Bharat2310/sih-2026/assets/screenshots/after_dac_waveform.jpeg

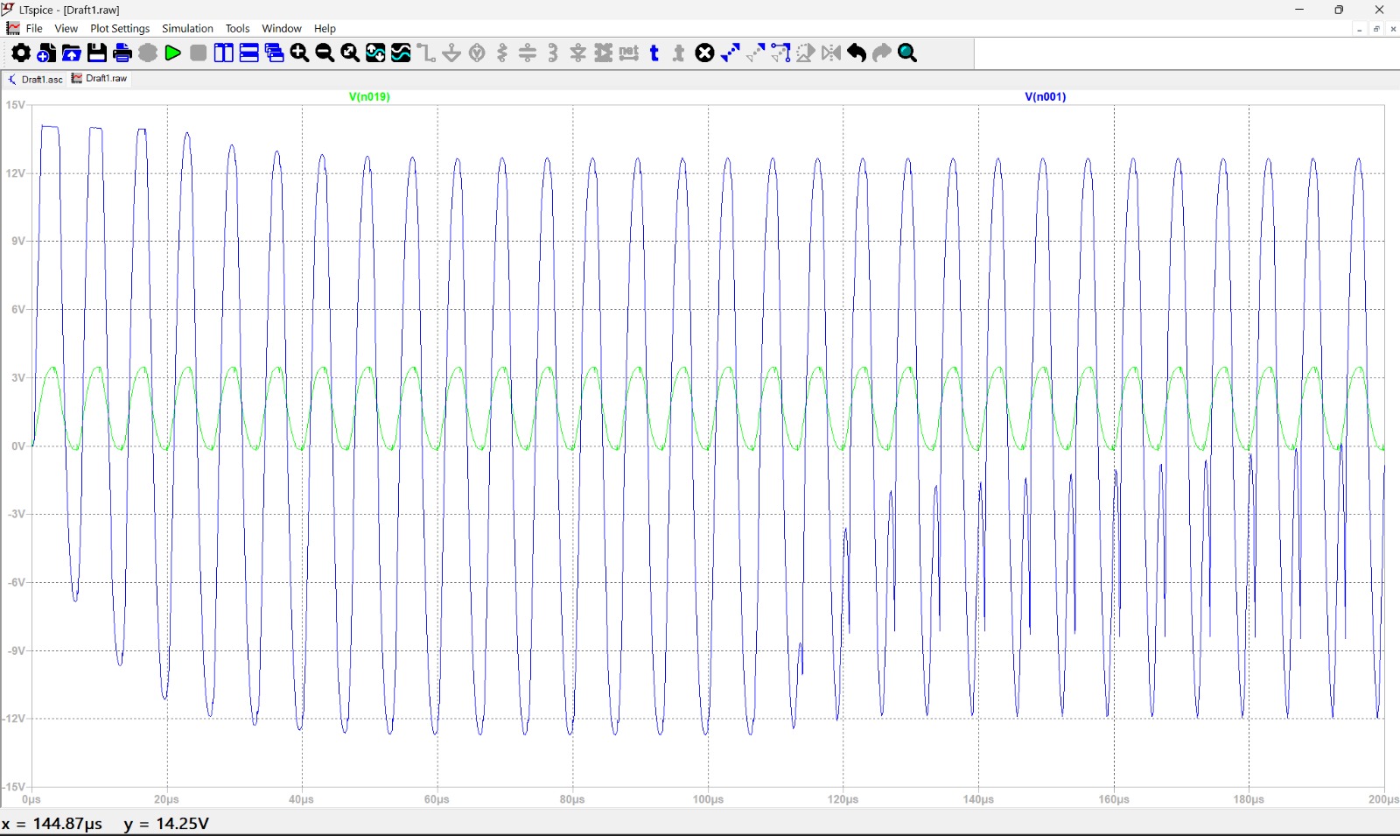
assets/screenshots/after_dac_waveform.jpeg
