Bharat2310/sih-2026/assets/screenshots/before_dac_full_pipeline.png

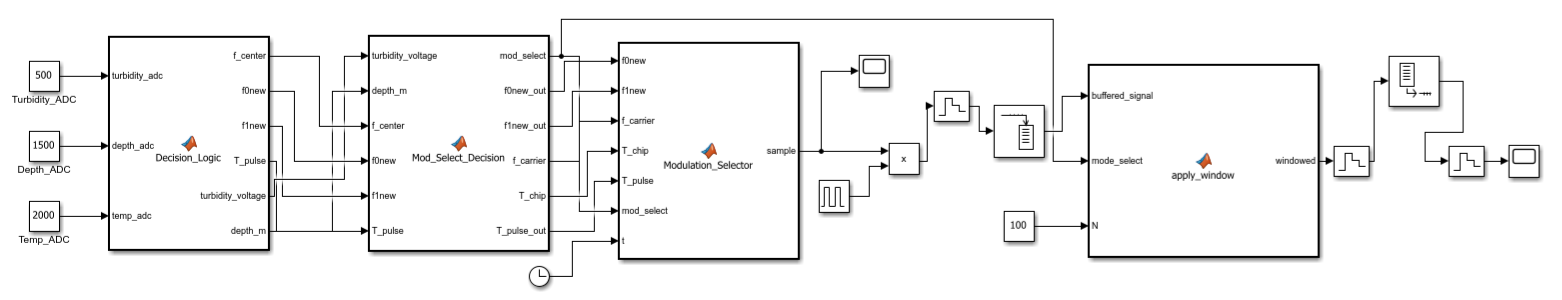
assets/screenshots/before_dac_full_pipeline.png
