Bharat2310/sih-2026/assets/screenshots/mod_select_decision.jpeg

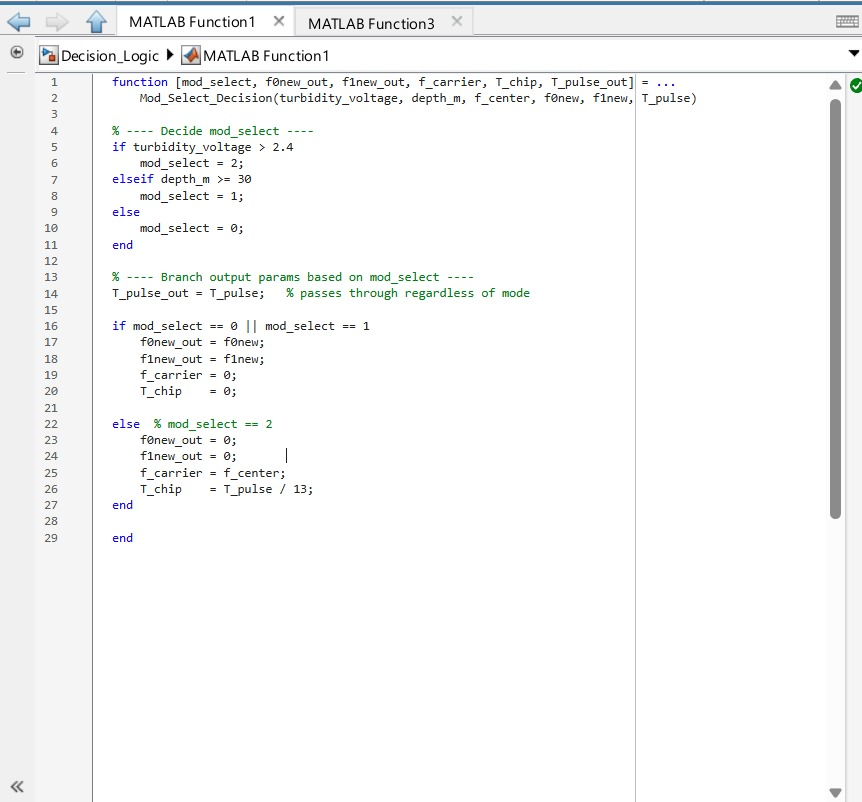
assets/screenshots/mod_select_decision.jpeg
