Bharat2310/sih-2026/assets/screenshots/mode0_lfm_final.jpeg

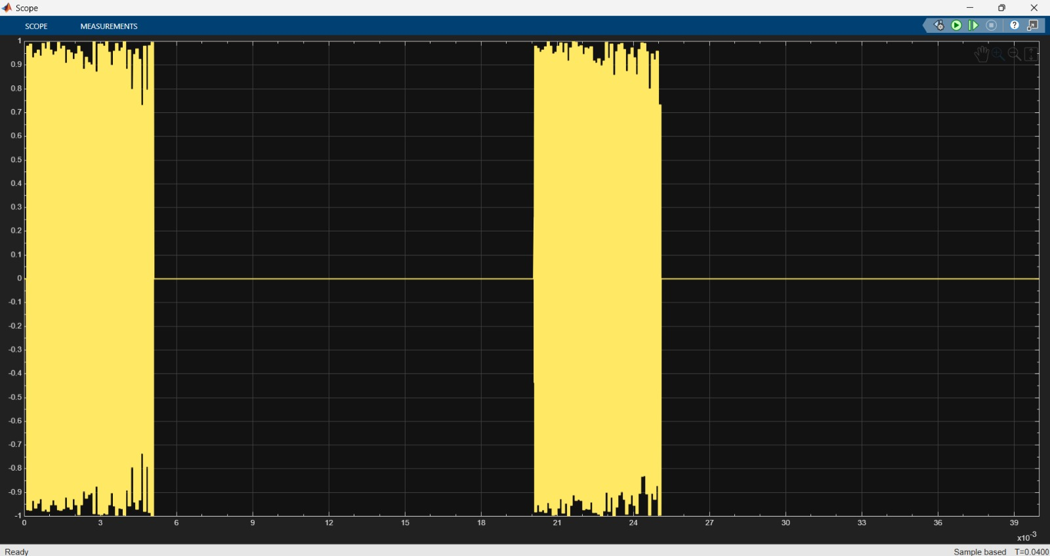
assets/screenshots/mode0_lfm_final.jpeg
