Bharat2310/sih-2026/assets/screenshots/mode2_phasecoded_raw.jpeg

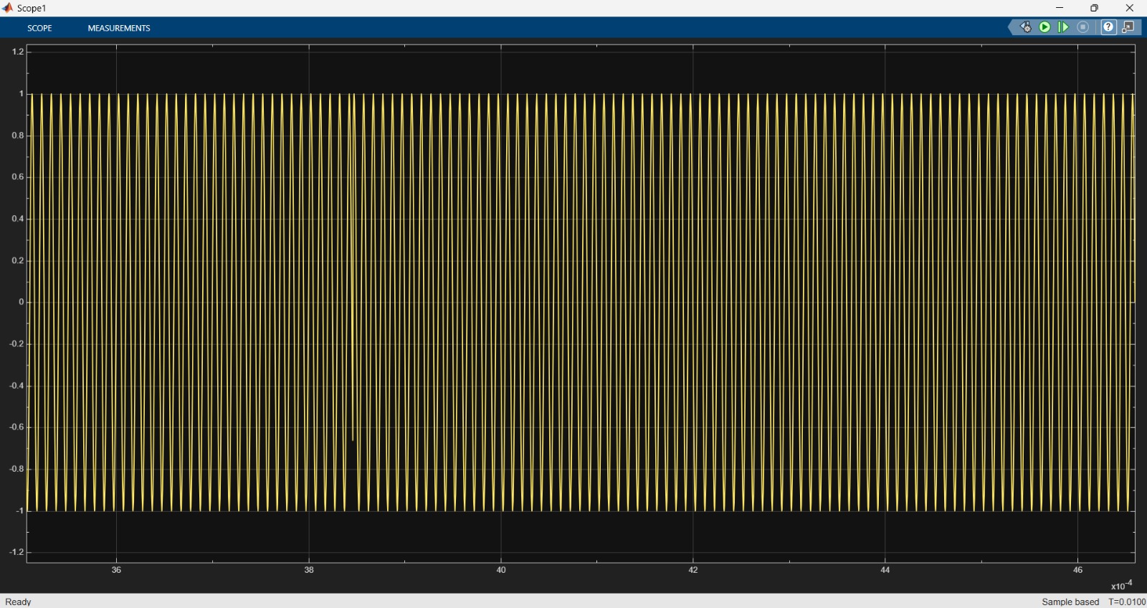
assets/screenshots/mode2_phasecoded_raw.jpeg
