Bharat2310/sih-2026/src/ltspice/after_dac_model.asc

C1: cap; 1n
C2: cap; 1n
C3: cap; 100p
C4: cap; 10µ
D1: diode
D2: diode
L1: ind; 11.26m
L2: ind; 1.126m
Q1: npn
Q2: pnp
R1: res; 10k
R2: res; 6.2k
R3: res; 1k
R4: res; 100
S1: sw; MUX
S2: sw; MUX
S3: sw; MUX
S4: sw; MUX
S5: sw; MUX
S6: sw; MUX
U1: LT1122
V1: voltage; PULSE(0 3.3 0 10n 10n 3.33u 6.66u)
V2: voltage; 0
V3: voltage; 3.3
V4: voltage; 0
V5: voltage; 5
V6: voltage; 18
V7: voltage; -18
V8: voltage; 18
V9: voltage; -18
V10: voltage; 15
V11: voltage; -15
X1: working_analog; R1=1k R2=1k C1=900p C2=500p
X2: working_analog; R1=1k R2=1k C1=500p C2=1000p
X3: working_analog; R1=300 R2=300 C1=470p C2=900p
Named nets: 0, CMD_CLEAR, CMD_MURKY, CMD_MUDDY, VCC
.model MUX SW(Ron=50 Roff=100Meg Vt=1.6)
.tran 0.2m
Simulated esp output waveform
MUX switches for routing 
signal to correct filter
2nd order 
Salllen key
butterworth filter
Class AB amplifier
Push-Pull Transistors
LC Networking
Transducer
