Bharat2310/sih-2026/src/ltspice/working_analog.asc

C1: cap; {C1}
C2: cap; {C2}
R1: res; {R1}
R2: res; {R2}
U1: LT1057
Named nets: 0, IN, OUT, Vcc, Vee
Low Pass Filter
